jmcpheron/open-studs/patterns/cluster.scad

// patterns/cluster.scad — small groups of studs with empty space between.
// MIT licensed.
//
// STUB. Signature locked; cluster topology TBD. Returns an empty list for now
// so the bracelet still compiles when this pattern is selected.

function pattern_cluster(band_length, band_width, rows = 1, spacing = undef) =
    [];  // TODO: design cluster topology
