jmcpheron/open-studs/patterns/gradient_size.scad

// patterns/gradient_size.scad — studs that grow/shrink along the band.
// MIT licensed.
//
// STUB. Signature locked; this pattern needs the position list to carry size
// info too (currently it only returns [x, y]). Likely a future-extension to
// allow [x, y, size_scale]. For now returns empty so bracelet still compiles.

function pattern_gradient_size(band_length, band_width, rows = 1, spacing = undef) =
    [];  // TODO: extend signature to carry per-stud size scale
